rlangoy/RCPico/images/IMG_20230708_105101.jpg

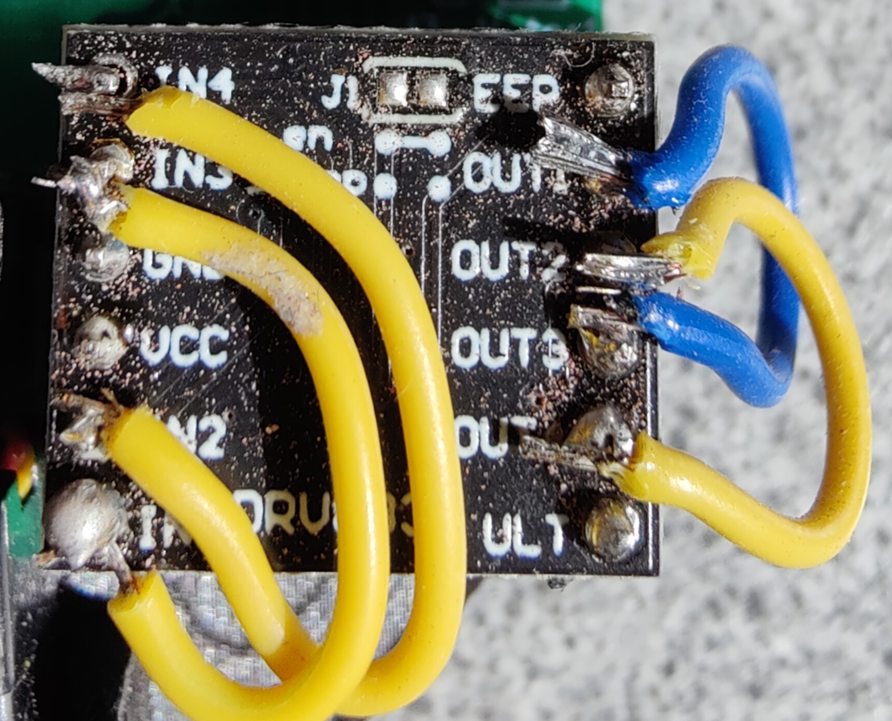
images/IMG_20230708_105101.jpg
