rlangoy/RCPico/MicroPython/WifiController/boot.py

import network

import gc
gc.collect()

ssid = 'GemmmaRC#01'
password = '123456789'

ap = network.WLAN(network.AP_IF)
ap.config(essid=ssid, password=password)
ap.active(True)
ap.config(essid=ssid, password=password)

while ap.active() == False:
  pass

print('Connection successful')
print(ap.ifconfig())
